thewinger/winsplit/resources/Keychron Q8 Keycap Size.webp

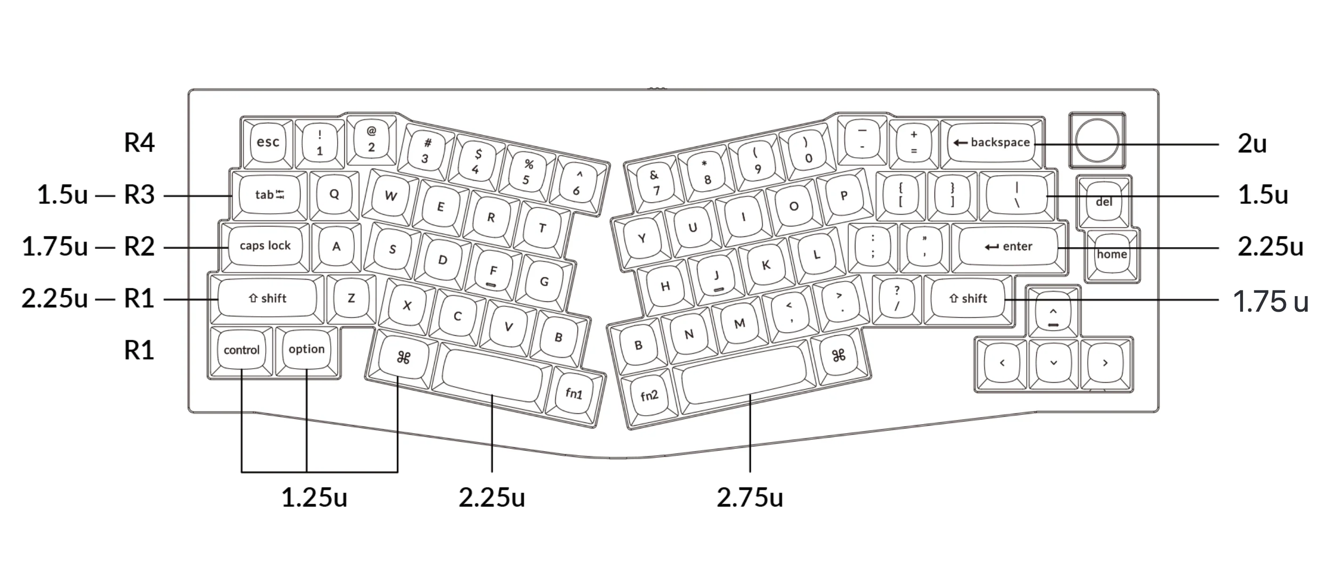
resources/Keychron Q8 Keycap Size.webp
