thewinger/winsplit/Resources/kicad_templates-master/Alchitry_Au/meta/board.png

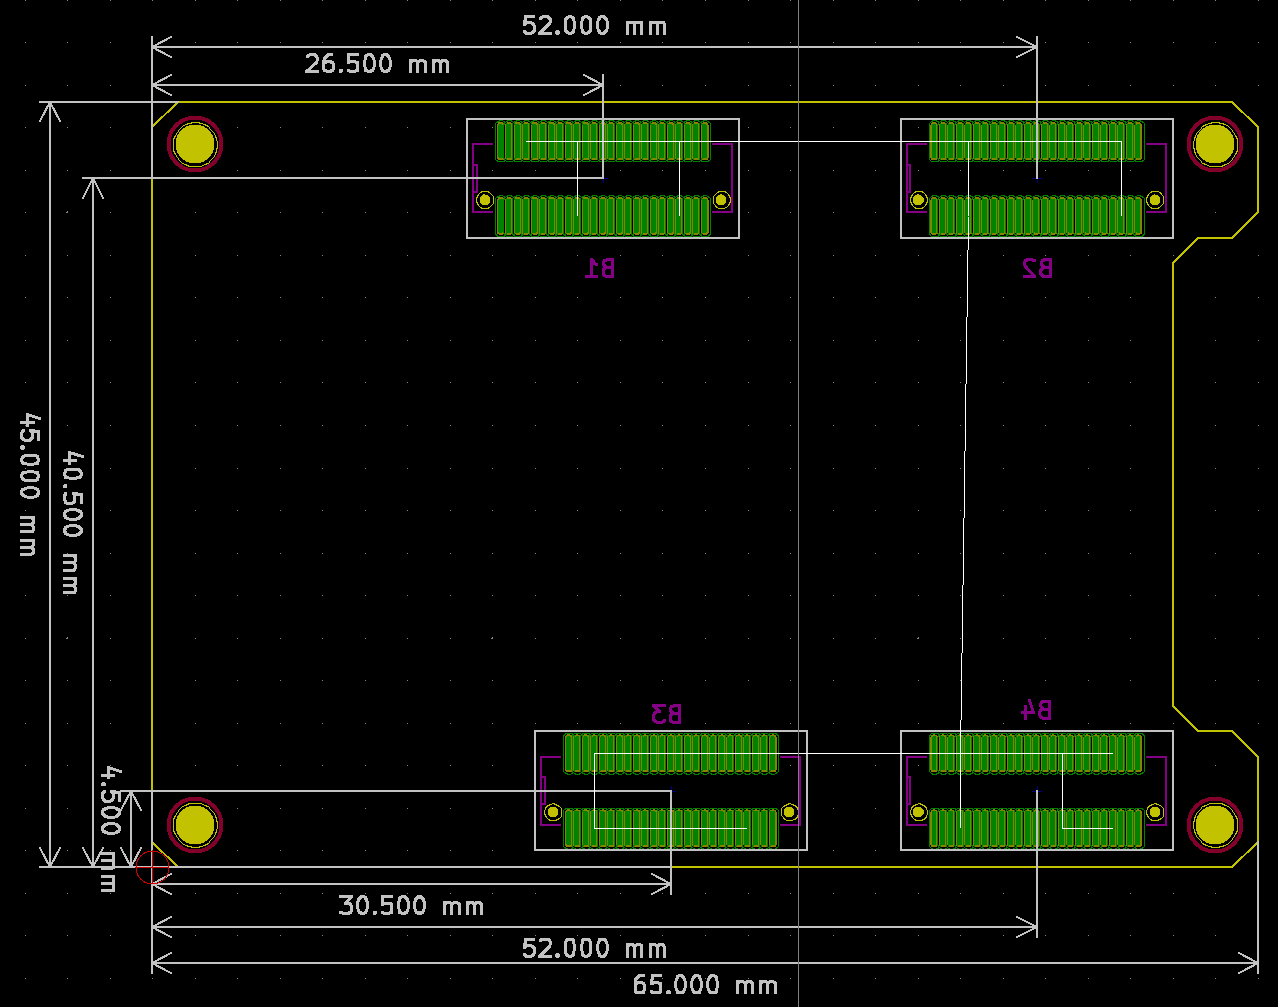
Resources/kicad_templates-master/Alchitry_Au/meta/board.png
