thewinger/winsplit/Resources/kicad_templates-master/Sierra 2 layer Board/meta/Images/Layers.JPG

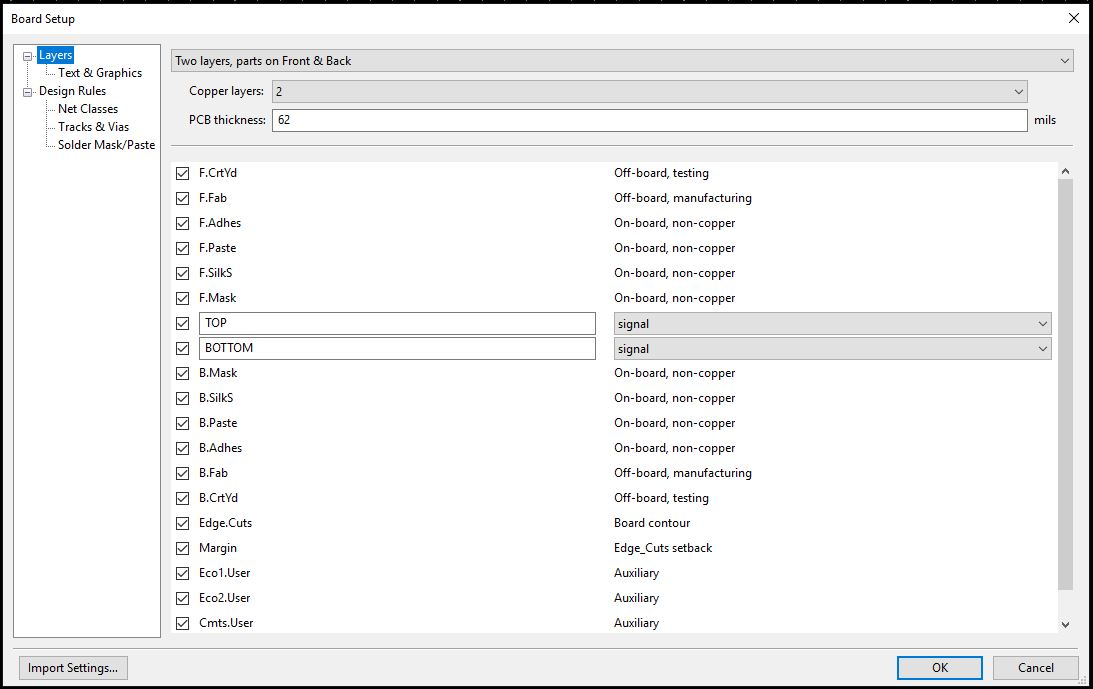
Resources/kicad_templates-master/Sierra 2 layer Board/meta/Images/Layers.JPG
