thewinger/winsplit/Resources/kicad_templates-master/Sierra 2 layer Board/meta/Images/layout.jpg

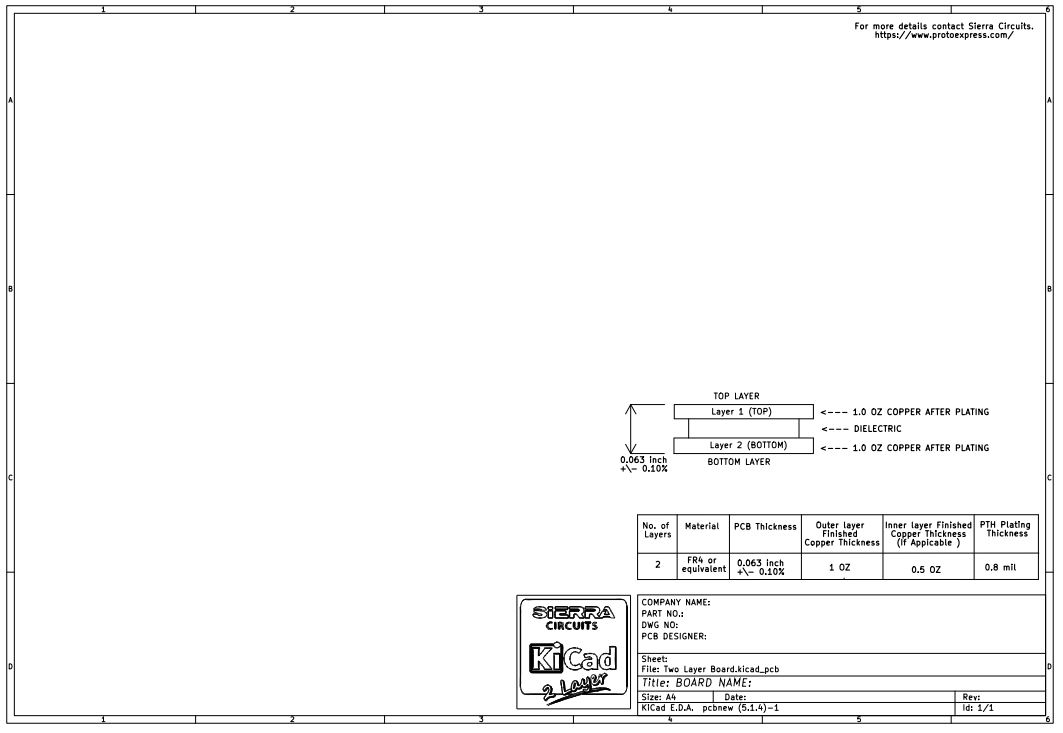
Resources/kicad_templates-master/Sierra 2 layer Board/meta/Images/layout.jpg
