thewinger/winsplit/Resources/kicad_templates-master/Sierra 2 layer Board/meta/Images/Net Classes.JPG

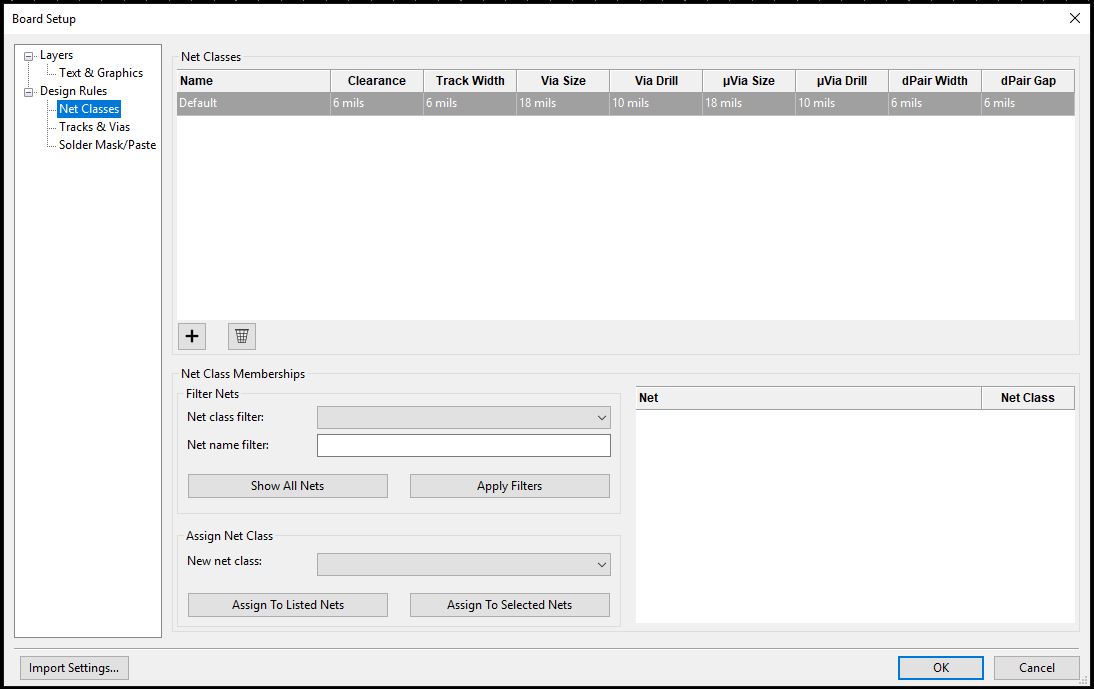
Resources/kicad_templates-master/Sierra 2 layer Board/meta/Images/Net Classes.JPG
