thewinger/winsplit/Resources/kicad_templates-master/Sierra 2 layer Board/meta/Images/schematic.jpg

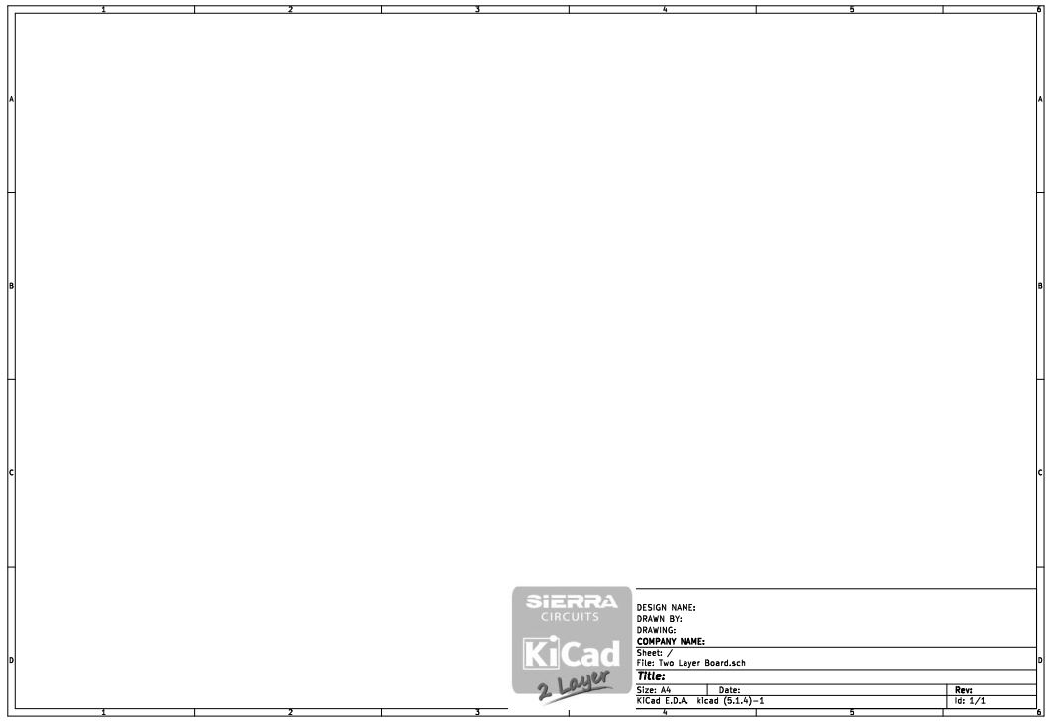
Resources/kicad_templates-master/Sierra 2 layer Board/meta/Images/schematic.jpg
