thewinger/winsplit/Resources/kicad_templates-master/Sierra 2 layer Board/meta/Images/Text & Graphics.JPG

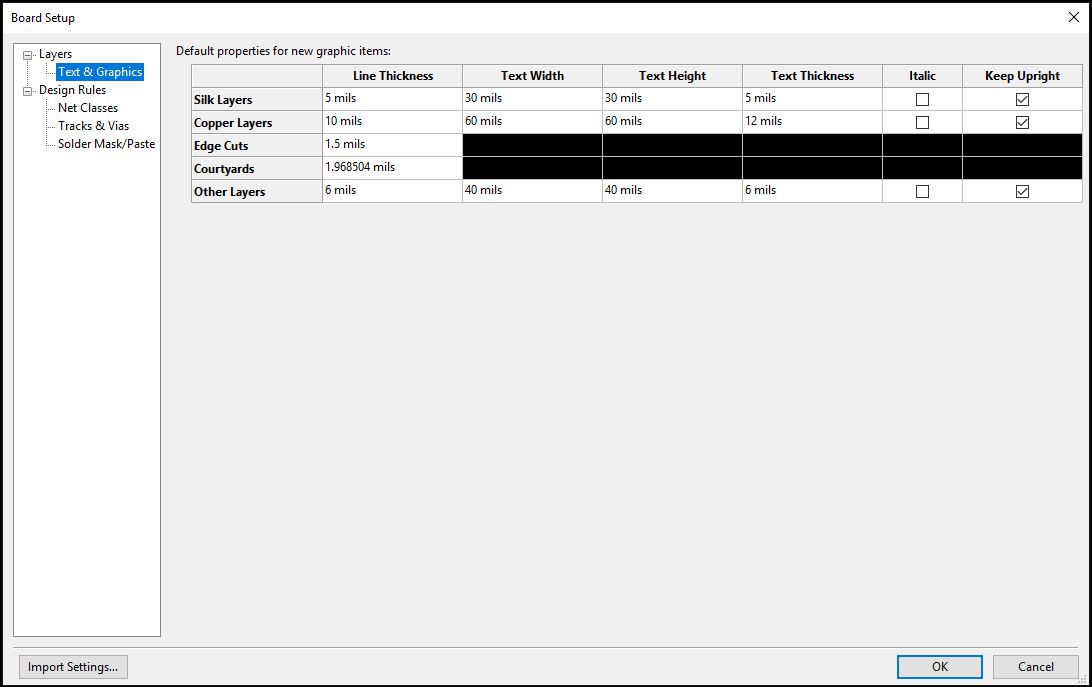
Resources/kicad_templates-master/Sierra 2 layer Board/meta/Images/Text & Graphics.JPG
