thewinger/winsplit/Resources/kicad_templates-master/Sierra 2 layer Board/meta/Images/Trace & Vias.JPG

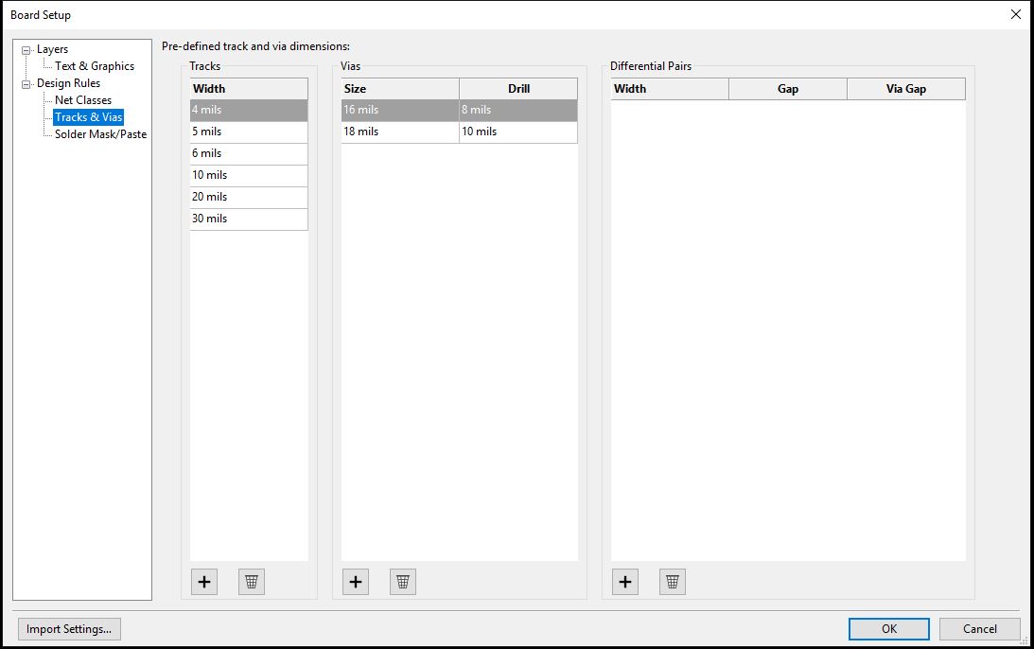
Resources/kicad_templates-master/Sierra 2 layer Board/meta/Images/Trace & Vias.JPG
