thewinger/winsplit/Resources/kicad_templates-master/Sierra 8 layer Board/meta/Images/layout.jpg

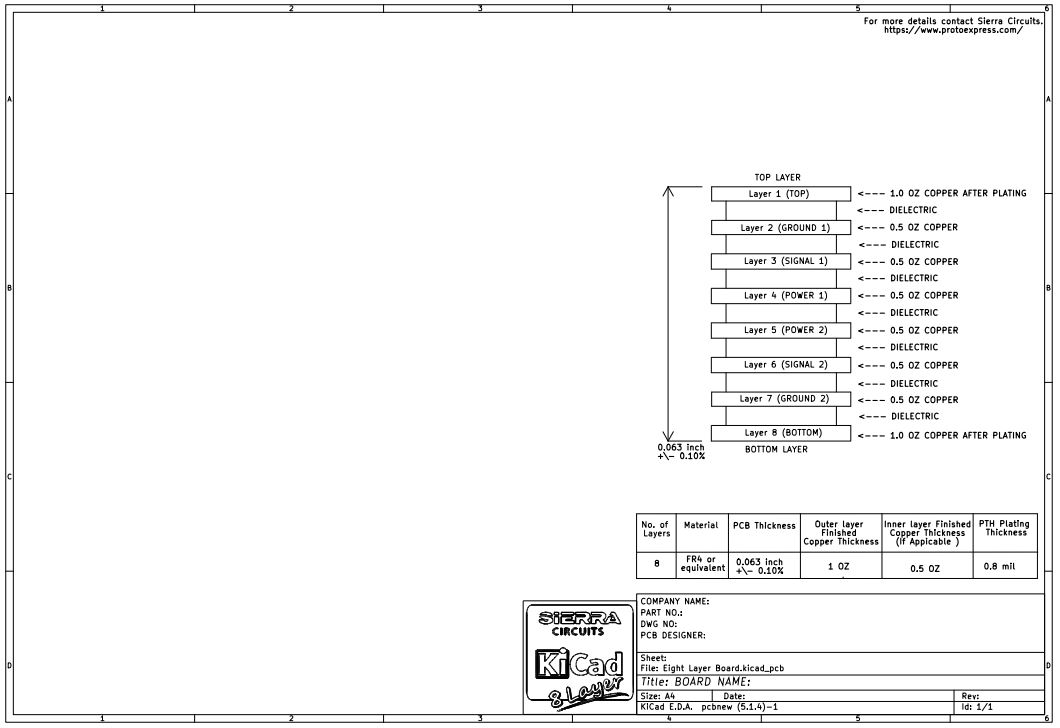
Resources/kicad_templates-master/Sierra 8 layer Board/meta/Images/layout.jpg
