thewinger/winsplit/Resources/kicad_templates-master/Sierra 12 layer Board/meta/Images/Layers.JPG

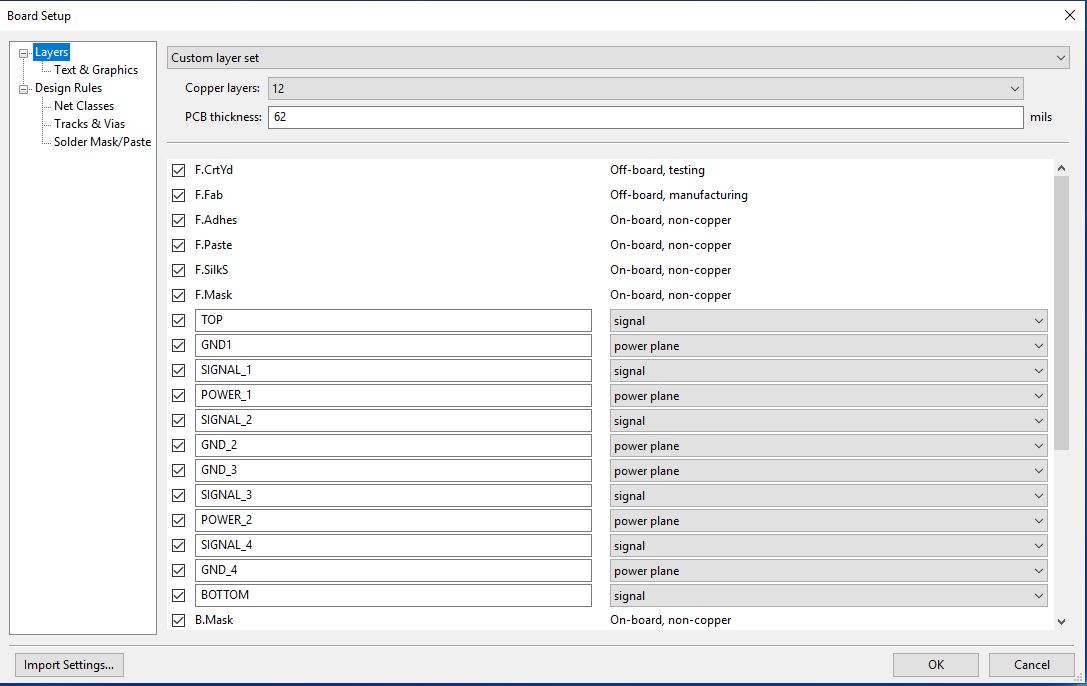
Resources/kicad_templates-master/Sierra 12 layer Board/meta/Images/Layers.JPG
