thewinger/winsplit/Resources/rp2040_promicro.png

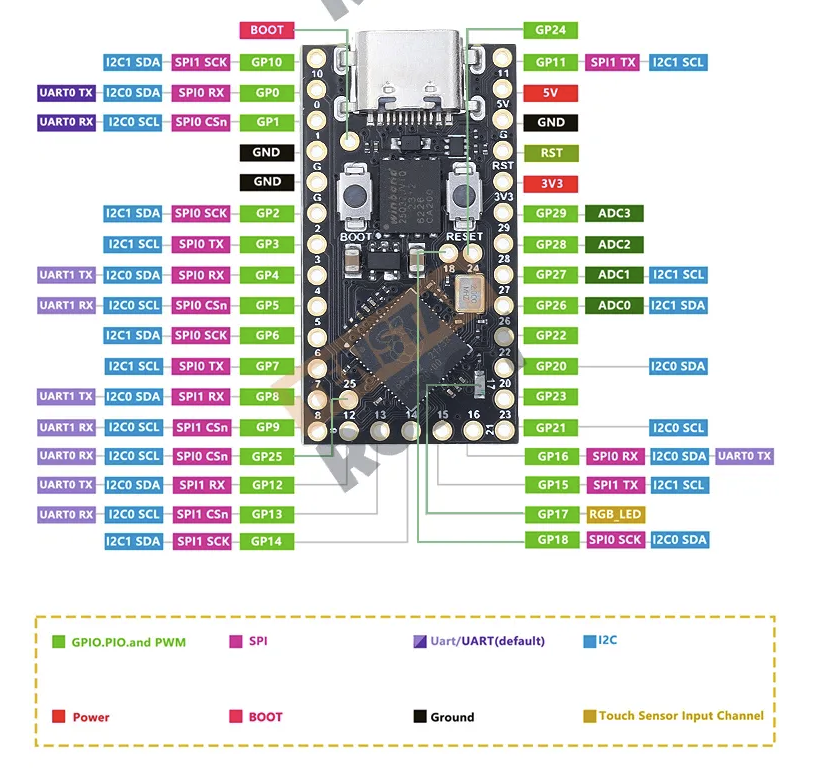
Resources/rp2040_promicro.png
